vsenger/Playground4IoT/arduino/Playground4IoTFirmware-V0/Logo_AWS.h

const uint8_t Logo_AWS[] PROGMEM ={
    0x00,0x00,0x00,0x00,0x00,0x00,0x00,0x78,0x7C,0x7C,0x7E,0x7E,0x3E,0x3F,0x3F,0x3F,
    0x3F,0x1F,0x1F,0x1F,0x1F,0x1F,0x1F,0x3F,0x3F,0x3F,0x7F,0xFF,0xFF,0xFE,0xFE,0xFC,
    0xFC,0xF8,0xF0,0xC0,0x00,0x00,0x00,0x06,0x1F,0xFF,0xFF,0xFF,0xFF,0xFF,0xFF,0xFE,
    0xF8,0xC0,0x00,0x00,0x00,0x00,0x00,0x00,0x00,0x00,0x00,0x00,0xE0,0xFC,0xFE,0xFF,
    0xFF,0xFF,0xFF,0xFF,0xFF,0xFE,0xF8,0xC0,0x00,0x00,0x00,0x00,0x00,0x00,0x00,0x00,
    0x00,0x00,0xC0,0xF8,0xFE,0xFF,0xFF,0xFF,0xFF,0xFF,0x3F,0x0E,0x00,0x00,0x00,0xC0,
    0xF0,0xF8,0xFC,0xFC,0xFE,0xFE,0xFF,0x7F,0x3F,0x3F,0x1F,0x1F,0x1F,0x1F,0x1F,0x1F,
    0x1F,0x1F,0x3F,0x3F,0x3F,0x3E,0x7E,0x7E,0x7C,0x00,0x00,0x00,0x00,0x00,0x00,0x00,
    0x00,0x00,0x00,0x00,0x00,0x00,0x00,0x00,0x00,0x80,0x80,0xC0,0xC0,0xE0,0xE0,0xE0,
    0xE0,0xE0,0xE0,0xE0,0xE0,0xE0,0xE0,0xE0,0xE0,0xE0,0xE0,0xC0,0xC7,0xFF,0xFF,0xFF,
    0xFF,0xFF,0xFF,0xFF,0x00,0x00,0x00,0x00,0x00,0x00,0x03,0x1F,0xFF,0xFF,0xFF,0xFF,
    0xFF,0xFF,0xFE,0xF0,0x80,0x00,0x00,0x00,0x00,0x80,0xF8,0xFF,0xFF,0xFF,0xFF,0xFF,
    0x1F,0x01,0x0F,0x7F,0xFF,0xFF,0xFF,0xFF,0xFE,0xE0,0x00,0x00,0x00,0x00,0x00,0x80,
    0xF0,0xFE,0xFF,0xFF,0xFF,0xFF,0xFF,0x7F,0x0F,0x01,0x00,0x00,0x00,0x00,0x00,0x0F,
    0x3F,0x7F,0xFF,0xFF,0xFF,0xFF,0xFF,0xF8,0xF8,0xF0,0xF0,0xF0,0xF0,0xE0,0xE0,0xE0,
    0xE0,0xC0,0xC0,0xC0,0x80,0x80,0x00,0x00,0x00,0x00,0x00,0x00,0x00,0x00,0x00,0x00,
    0x00,0x00,0x00,0x00,0x00,0xF0,0xFC,0xFE,0xFF,0xFF,0xFF,0xFF,0xFF,0x1F,0x0F,0x07,
    0x07,0x03,0x03,0x03,0x03,0x03,0x03,0x03,0x03,0x03,0x03,0x07,0xC7,0xFF,0xFF,0xFF,
    0xFF,0xFF,0xFF,0xFF,0x00,0x00,0x00,0x00,0x00,0x00,0x00,0x00,0x00,0x03,0x1F,0xFF,
    0xFF,0xFF,0xFF,0xFF,0xFF,0xF8,0x80,0xC0,0xFC,0xFF,0xFF,0xFF,0xFF,0x7F,0x0F,0x00,
    0x00,0x00,0x00,0x00,0x07,0x3F,0xFF,0xFF,0xFF,0xFF,0xFF,0xF0,0x00,0xE0,0xFC,0xFF,
    0xFF,0xFF,0xFF,0xFF,0x3F,0x0F,0x01,0x00,0x00,0x00,0x00,0x00,0x00,0x00,0x00,0x00,
    0x00,0x00,0x00,0x00,0x01,0x01,0x03,0x03,0x03,0x07,0x07,0x07,0x07,0x0F,0x0F,0x0F,
    0x0F,0x1F,0x3F,0xFF,0xFF,0xFF,0xFF,0xFF,0xFE,0xFC,0xF0,0x00,0x00,0x00,0x00,0x00,
    0x00,0x00,0x00,0x00,0x00,0x07,0x0F,0x3F,0x3F,0x7F,0xFF,0xFF,0xFF,0xFF,0xFC,0xF8,
    0xF8,0xF8,0xF8,0xF8,0xF8,0xF8,0xF8,0xF8,0x7C,0x7C,0x3E,0x3F,0x1F,0x0F,0x3F,0x7F,
    0xFF,0xFF,0xFF,0x7F,0x78,0x30,0x00,0x00,0x00,0x00,0x00,0x00,0x00,0x00,0x00,0x00,
    0x03,0x1F,0x7F,0xFF,0xFF,0xFF,0xFF,0xFF,0xFF,0xFF,0xFF,0x3F,0x07,0x00,0x00,0x00,
    0x00,0x00,0x00,0x00,0x00,0x00,0x03,0x1F,0x7F,0xFF,0xFF,0xFF,0xFF,0xFF,0xFF,0xFF,
    0xFF,0x3F,0x0F,0x01,0x00,0x00,0x00,0x00,0x00,0x00,0x00,0x00,0x00,0x00,0x3C,0x7E,
    0x7E,0x7C,0xFC,0xFC,0xFC,0xF8,0xF8,0xF8,0xF8,0xF8,0xF8,0xF8,0xF8,0xF8,0xF8,0xF8,
    0xF8,0xFC,0xFE,0xFF,0x7F,0x7F,0x3F,0x3F,0x1F,0x0F,0x03,0x00,0x00,0x00,0x00,0x00,
    0x00,0x00,0x00,0x00,0x00,0x00,0x00,0x00,0x00,0x00,0x00,0x00,0x00,0x01,0x01,0x01,
    0x01,0x01,0x01,0x01,0x01,0x00,0x00,0x00,0x00,0x00,0x00,0x00,0x00,0x00,0x00,0x00,
    0x00,0x00,0x00,0x00,0x00,0x00,0x00,0x00,0x00,0x00,0x00,0x00,0x00,0x00,0x00,0x00,
    0x00,0x00,0x00,0x00,0x00,0x00,0x00,0x00,0x00,0x00,0x00,0x00,0x00,0x00,0x00,0x00,
    0x00,0x00,0x00,0x00,0x00,0x00,0x00,0x00,0x00,0x00,0x00,0x00,0x00,0x00,0x00,0x00,
    0x00,0x00,0x00,0x00,0x00,0x00,0x00,0x00,0x00,0x00,0x00,0x00,0x00,0x00,0x00,0x00,
    0x00,0x00,0x00,0x00,0x00,0x00,0x01,0x01,0x01,0x01,0x01,0x01,0x01,0x81,0x81,0x81,
    0x80,0xC0,0xC0,0xC0,0xC0,0xC0,0xC0,0xC0,0xC0,0xC0,0xC0,0xC0,0xC0,0x80,0x80,0x00,
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
};
