vsenger/Playground4IoT/arduino/Playground4IoTFirmware-V0/TSL2571.ino

void le_TSL2571(){
    // Start I2C Transmission
    Wire.beginTransmission(Addr);
    // Select data register
    Wire.write(0x14 | 0x80);
    // Stop I2C Transmission
    Wire.endTransmission();
    
    // Request 4 bytes of data
    Wire.requestFrom(Addr, 4);
    
    // Read 4 bytes of data
    // c0Data lsb, c0Data msb, c1Data lsb, c1Data msb
    if(Wire.available() == 4){
      data[0] = Wire.read();
      data[1] = Wire.read();
      data[2] = Wire.read();
      data[3] = Wire.read();
    }

    // Convert the data
    int c0Data = (data[1] * 256) + data[0];
    int c1Data = (data[3] * 256) + data[2];
    float CPL = (2.72 * 1.0) / 53.0;
    float luminance1 = (1 * c0Data - 2.0 * c1Data) / CPL;
    float luminance2 = (0.6 * c0Data - 1.00 * c1Data) / CPL;
    float luminance = 0.0;
    
    if((luminance1 > 0) && (luminance1 > luminance2)){
      luminance = luminance1;
    }
    else if((luminance2 > 0) && (luminance2 > luminance1)){
      luminance = luminance2;
    }
    Luminosidade= luminance;
    Serial.print("Luminosidade:");
    Serial.println(Luminosidade);
    oledLuminosidade();
}




void init_TSL2571(){
    // Start I2C Transmission
    Wire.beginTransmission(Addr);
    // Select enable register
    Wire.write(0x00 | 0x80);
    // Set power on, ALS enabled
    Wire.write(0x01);
    // Stop I2C Transmission
    Wire.endTransmission();
    delay(500);

    // Start I2C Transmission
    Wire.beginTransmission(Addr);
    // Select enable register
    Wire.write(0x00 | 0x80);
    // Set power on, ALS enabled
    Wire.write(0x0B);
    // Stop I2C Transmission
    Wire.endTransmission();

    // Start I2C Transmission
    Wire.beginTransmission(Addr);
    // Select ALS time register
    Wire.write(0x01 | 0x80);
    // Atime = 2.72 ms, max count = 1023
    Wire.write(0xFF);
    // Stop I2C Transmission
    Wire.endTransmission();

    // Start I2C Transmission
    Wire.beginTransmission(Addr);
    // Select Wait time register
    Wire.write(0x03 | 0x80);
    // Wtime = 2.72 ms
    Wire.write(0xFF);
    // Stop I2C Transmission
    Wire.endTransmission();

    // Start I2C Transmission
    Wire.beginTransmission(Addr);
    // Select control register
    Wire.write(0x0F | 0x80);
    // Gain = 1x
    Wire.write(0x20);
    // Stop I2C Transmission
    Wire.endTransmission();
    delay(300);
}
